MDMohiUddinKhan/Basic-Calculator-Design-using-Logic-Gates/PCB design/Multiplier unit PCB (Size_8.1 inch x 8.7 inch)/Multiplier PCB Via (Top View).pdf

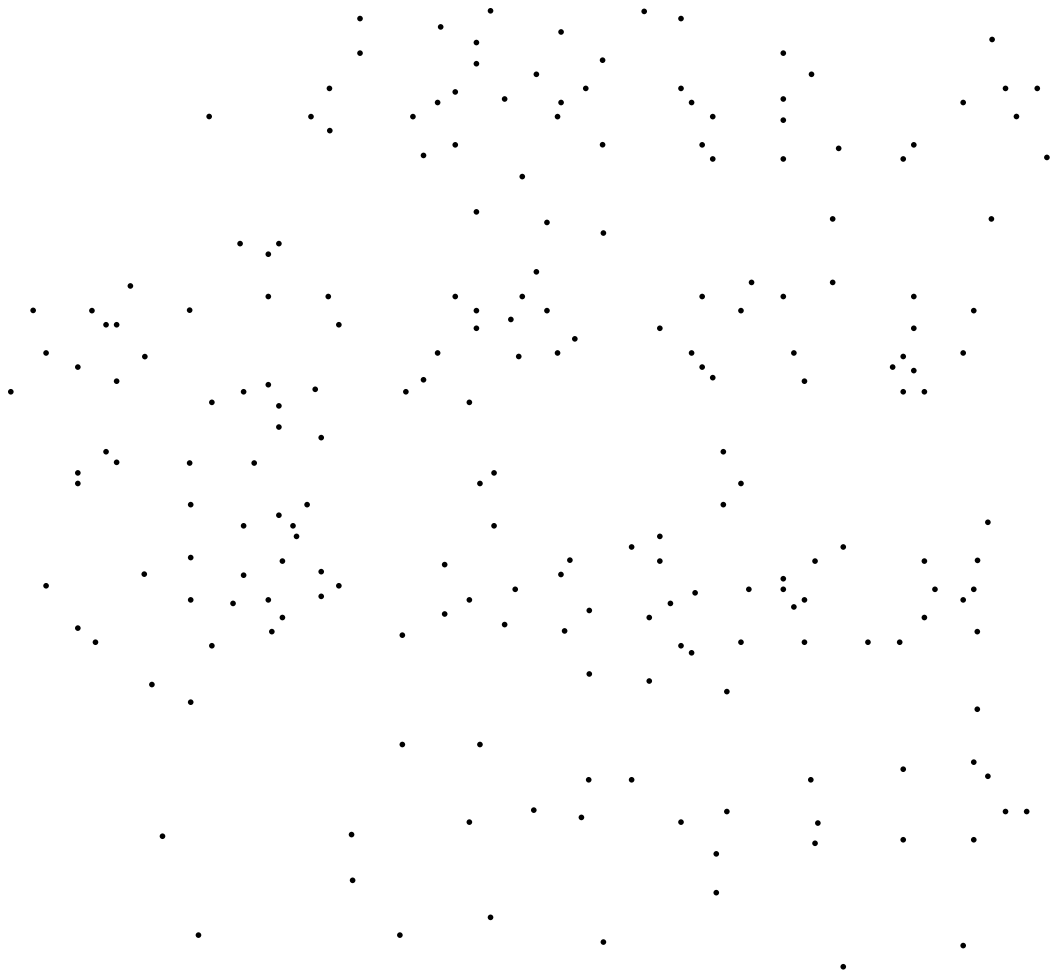
[picture p41: page 1]
