MDMohiUddinKhan/Basic-Calculator-Design-using-Logic-Gates/PCB design/Sample Efficient PCB design Multiplier unit PCB (Size_8.1 inch x 8.7 inch)/Multiplier PCB.pdf

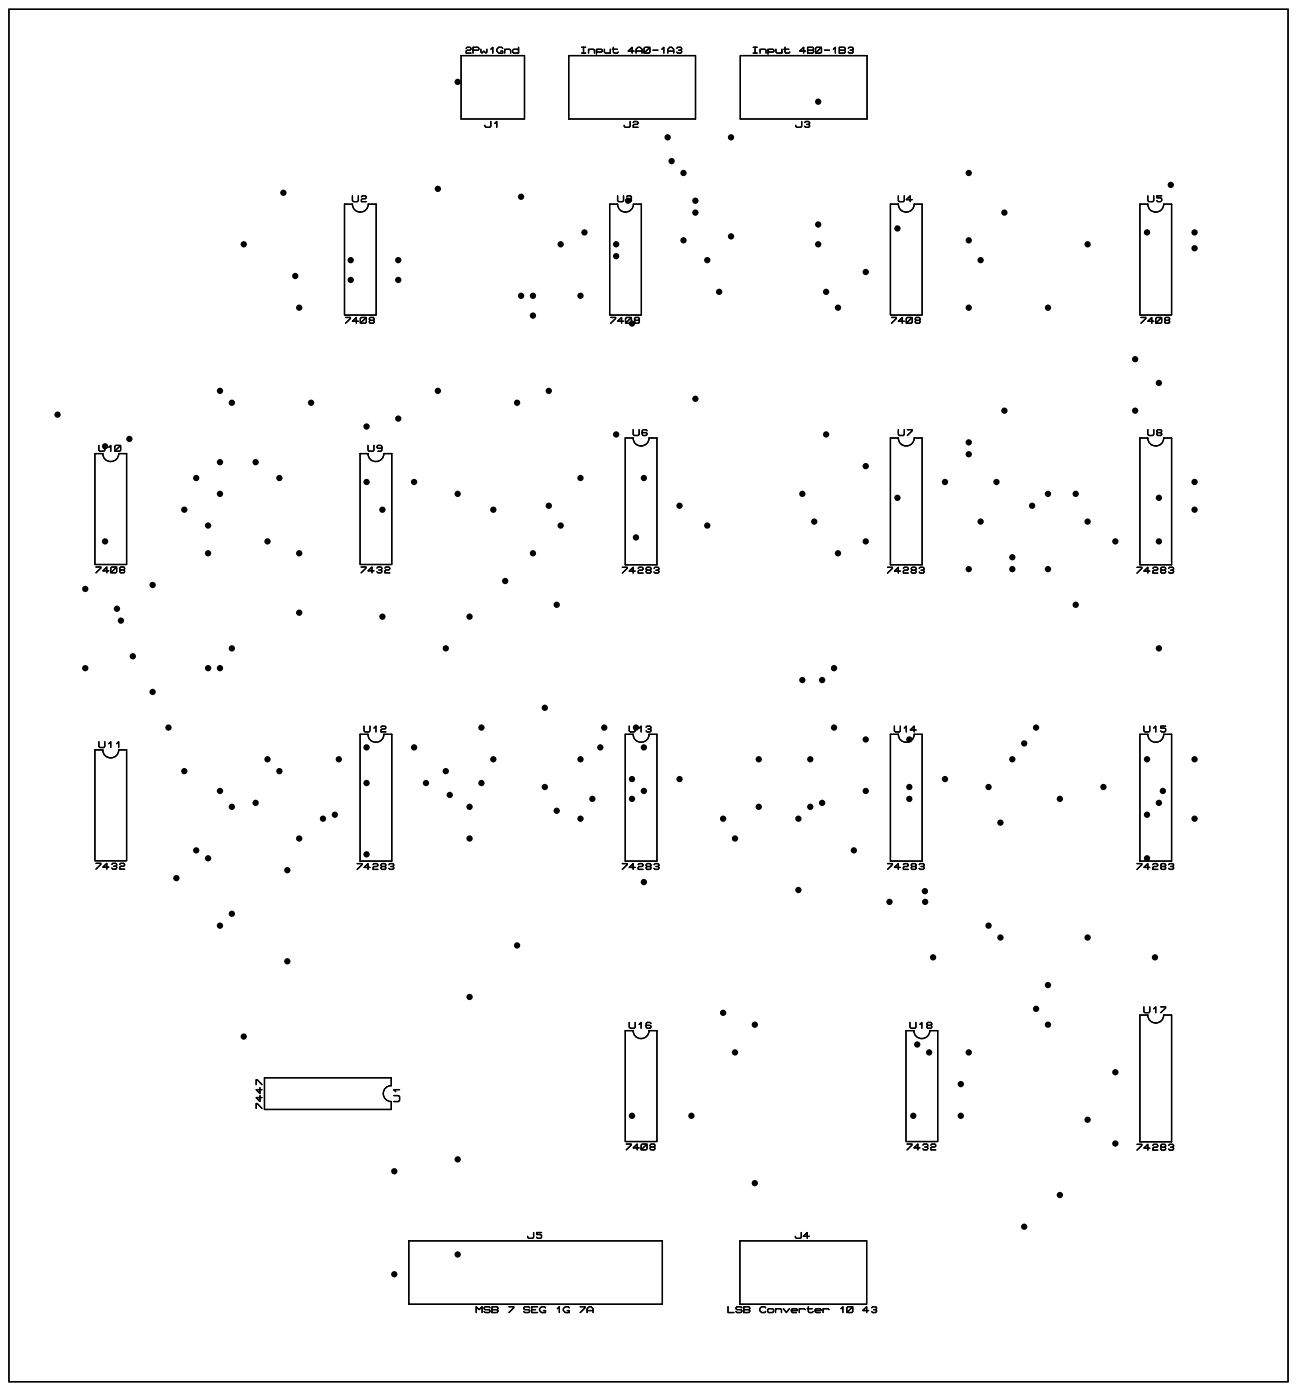
[picture p42: page 1]
